rusaakkmods/megamidimerge/docs/schematics/clock_out.png

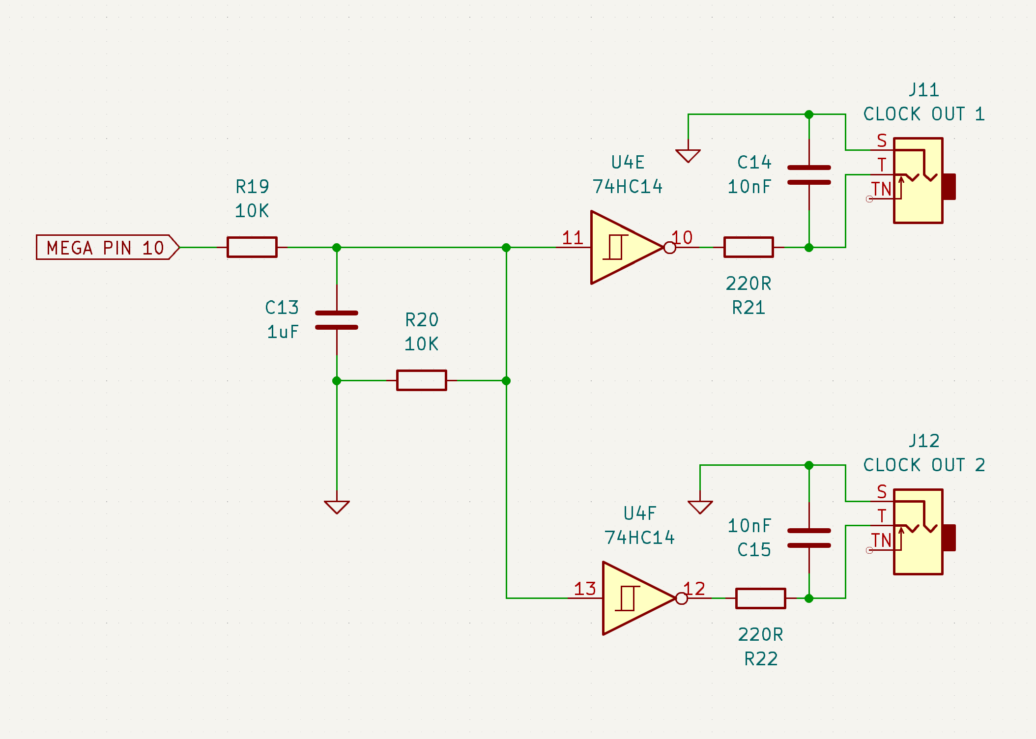
docs/schematics/clock_out.png
