rusaakkmods/megamidimerge/docs/schematics/master_switch.png

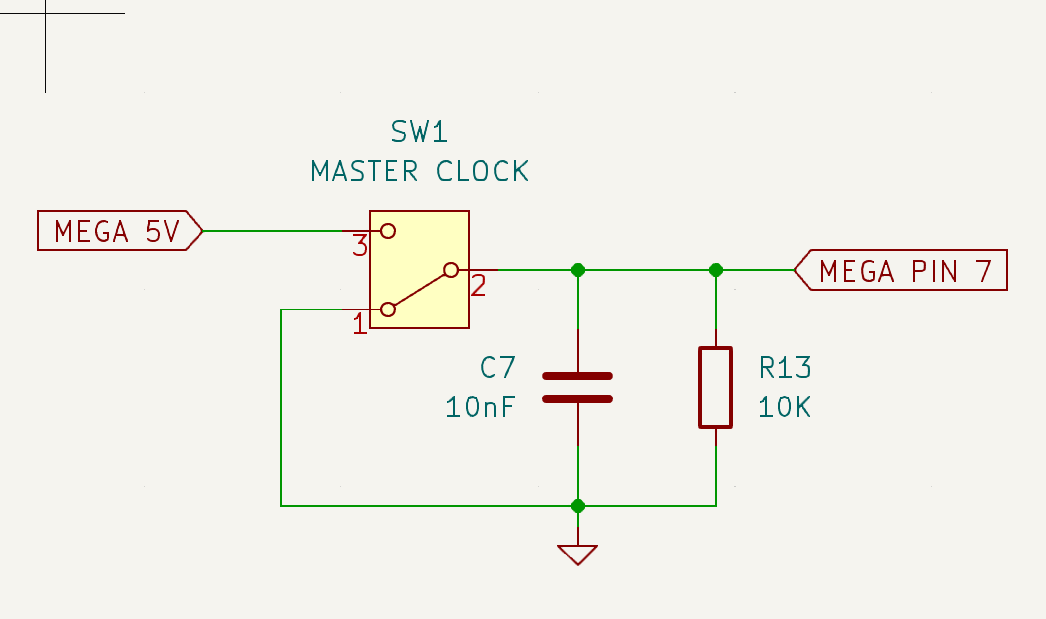
docs/schematics/master_switch.png
