rusaakkmods/megamidimerge/docs/schematics/midi_input.png

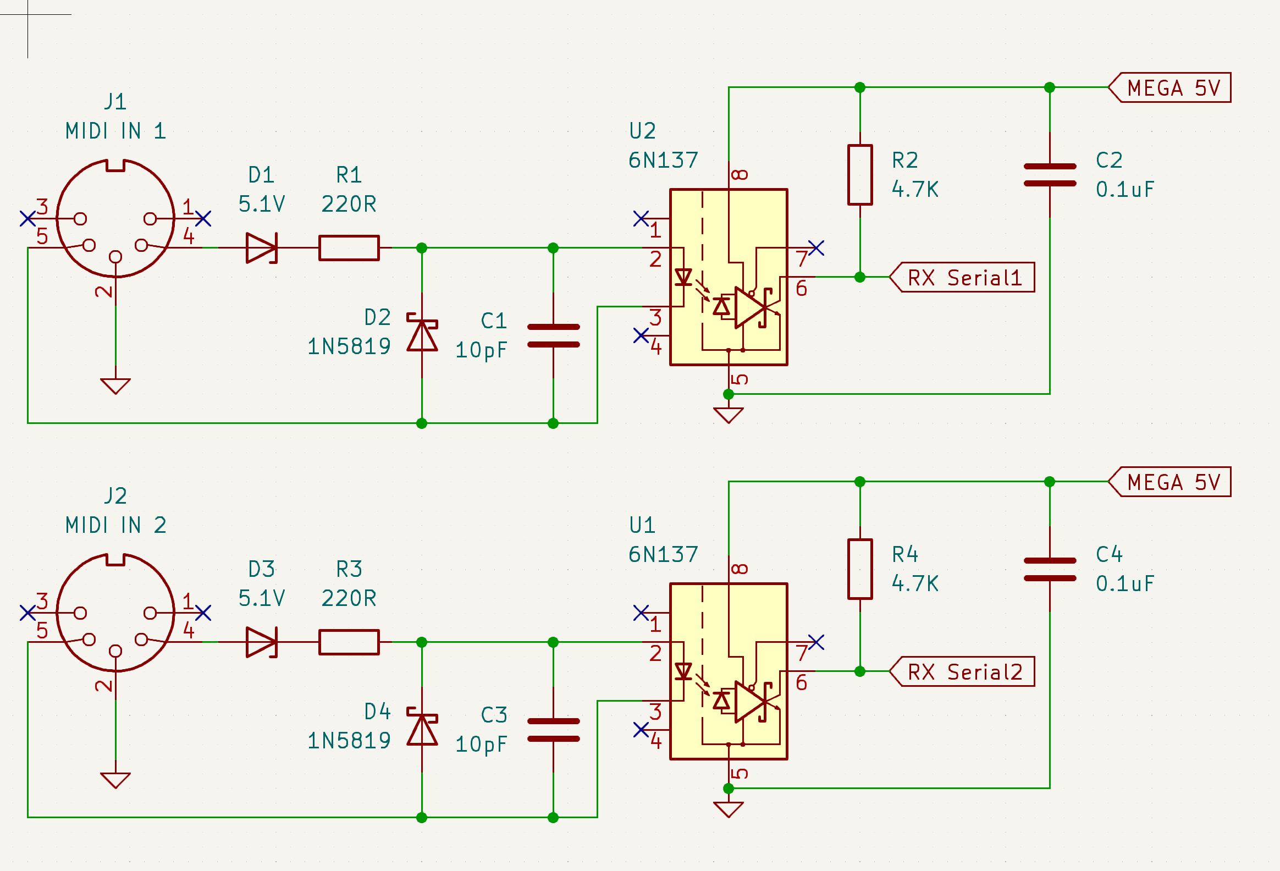
docs/schematics/midi_input.png
